ColbyDAllen/Wearable-Drum-Machine/Version 2/Software/WearableDrumMachine_RevB3/LoopedNoteFunctions.h

// LoopedNoteFuncs.h
#ifndef LOOPED_NOTE_FUNCS_H
#define LOOPED_NOTE_FUNCS_H

void myNoteOnLooped(byte channel, byte note, byte velocity);
void myNoteOffLooped(byte channel, byte note, byte velocity);

#endif
